getlarge/Cosmonode_PCBs/Cosmonode_ext02/docs/Cosmonode_ext02.png

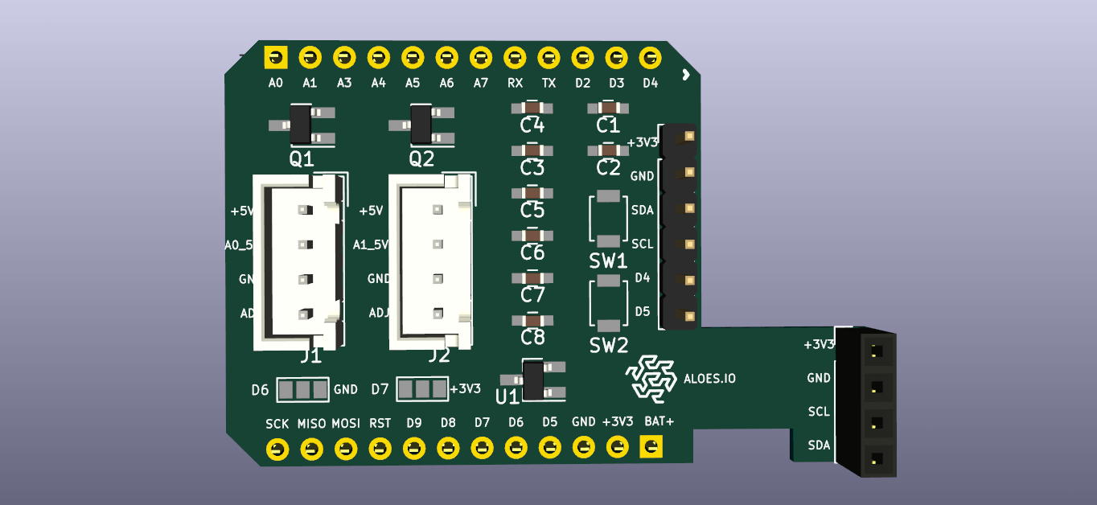
Cosmonode_ext02/docs/Cosmonode_ext02.png
