getlarge/Cosmonode_PCBs/Cosmonode_ext03/docs/Cosmonode_ext03.png

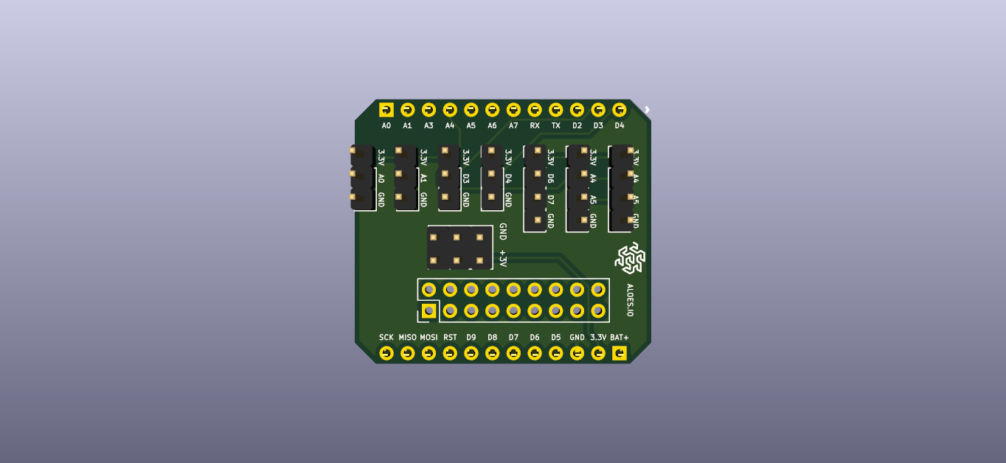
Cosmonode_ext03/docs/Cosmonode_ext03.png
