getlarge/Cosmonode_PCBs/Cosmonode_ext04/Cosmonode_ext_04.png

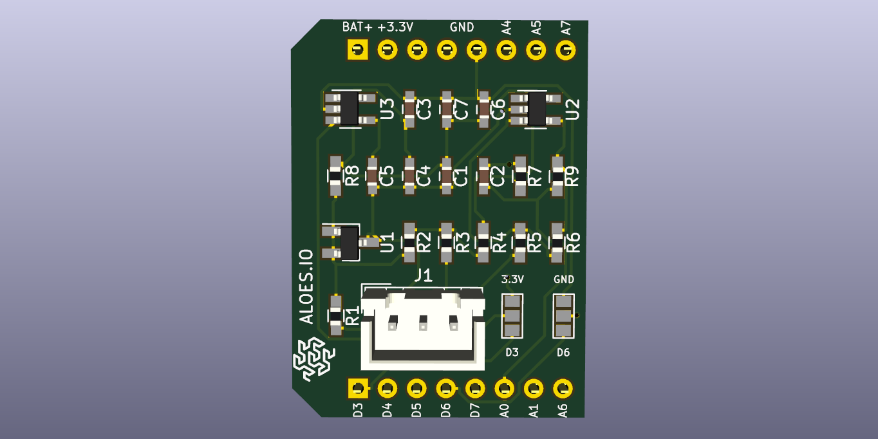
Cosmonode_ext04/Cosmonode_ext_04.png
