getlarge/Cosmonode_PCBs/Cosmonode_ext05/Cosmonode_ext05.png

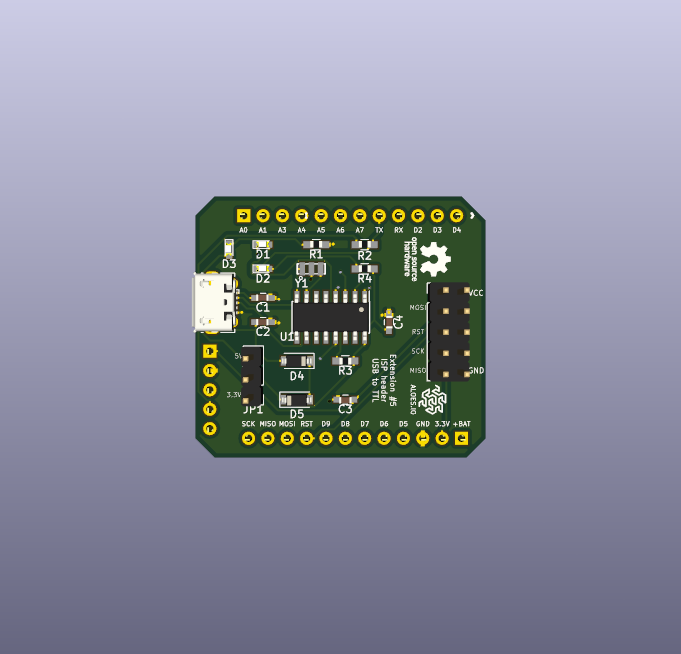
Cosmonode_ext05/Cosmonode_ext05.png
