getlarge/Cosmonode_PCBs/Cosmonode_ext06/Cosmonode_ext06.png

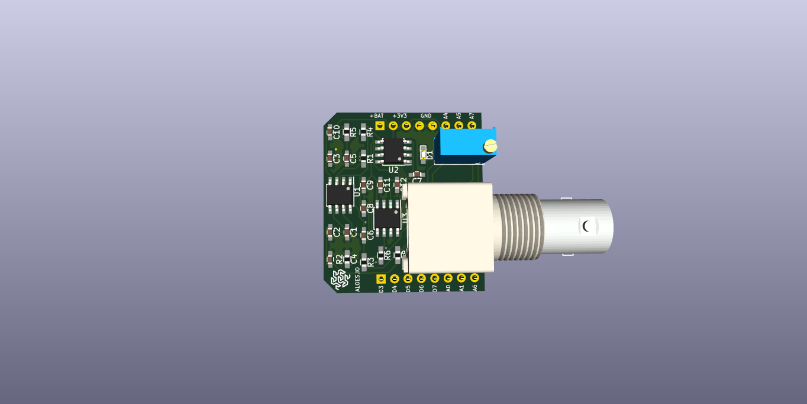
Cosmonode_ext06/Cosmonode_ext06.png
