getlarge/Cosmonode_PCBs/Cosmonode_ext07/Cosmonode_ext07.png

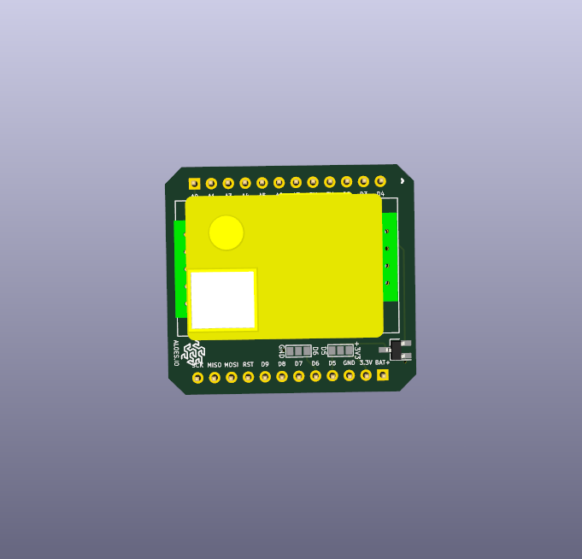
Cosmonode_ext07/Cosmonode_ext07.png
