getlarge/Cosmonode_PCBs/Cosmonode/docs/pcb.pdf

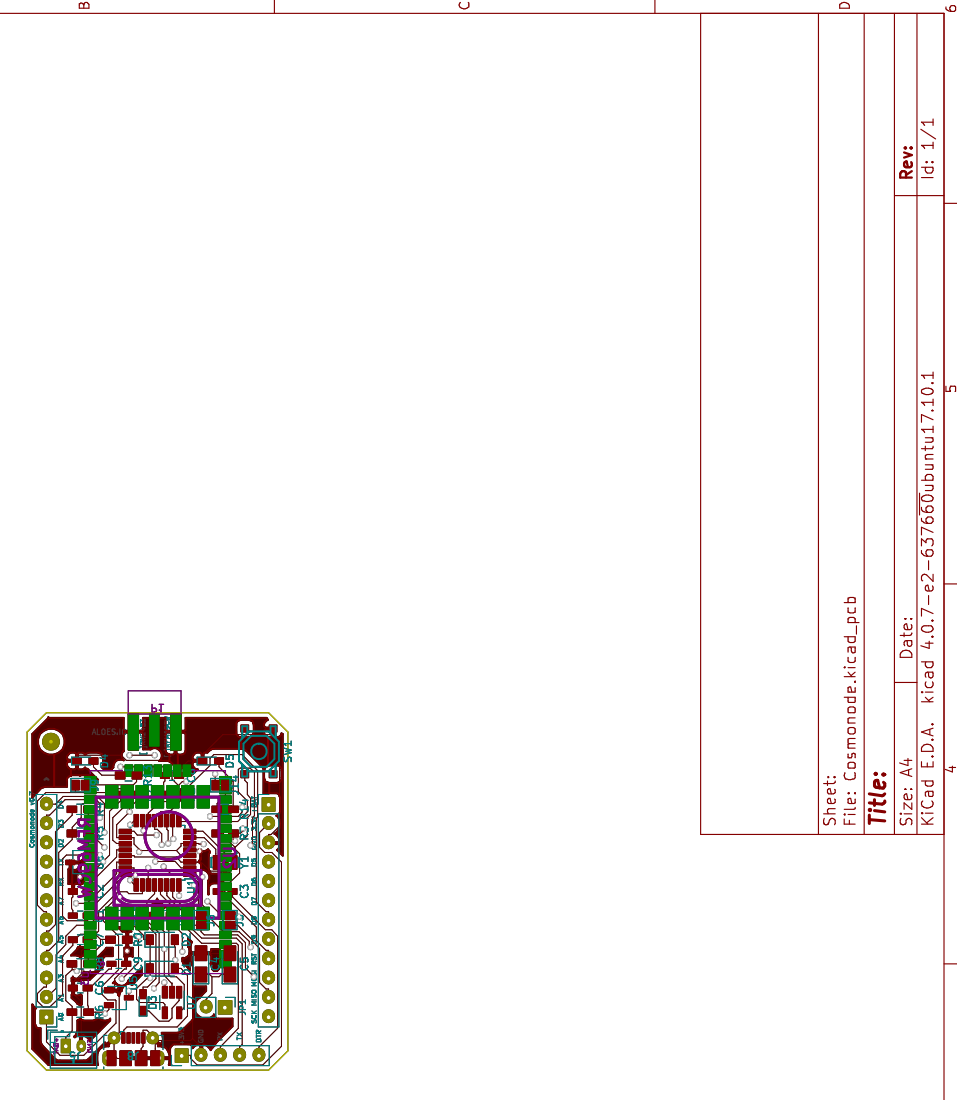
[picture p26: page 1]
