getlarge/Cosmonode_PCBs/Cosmonode/docs/schema.pdf

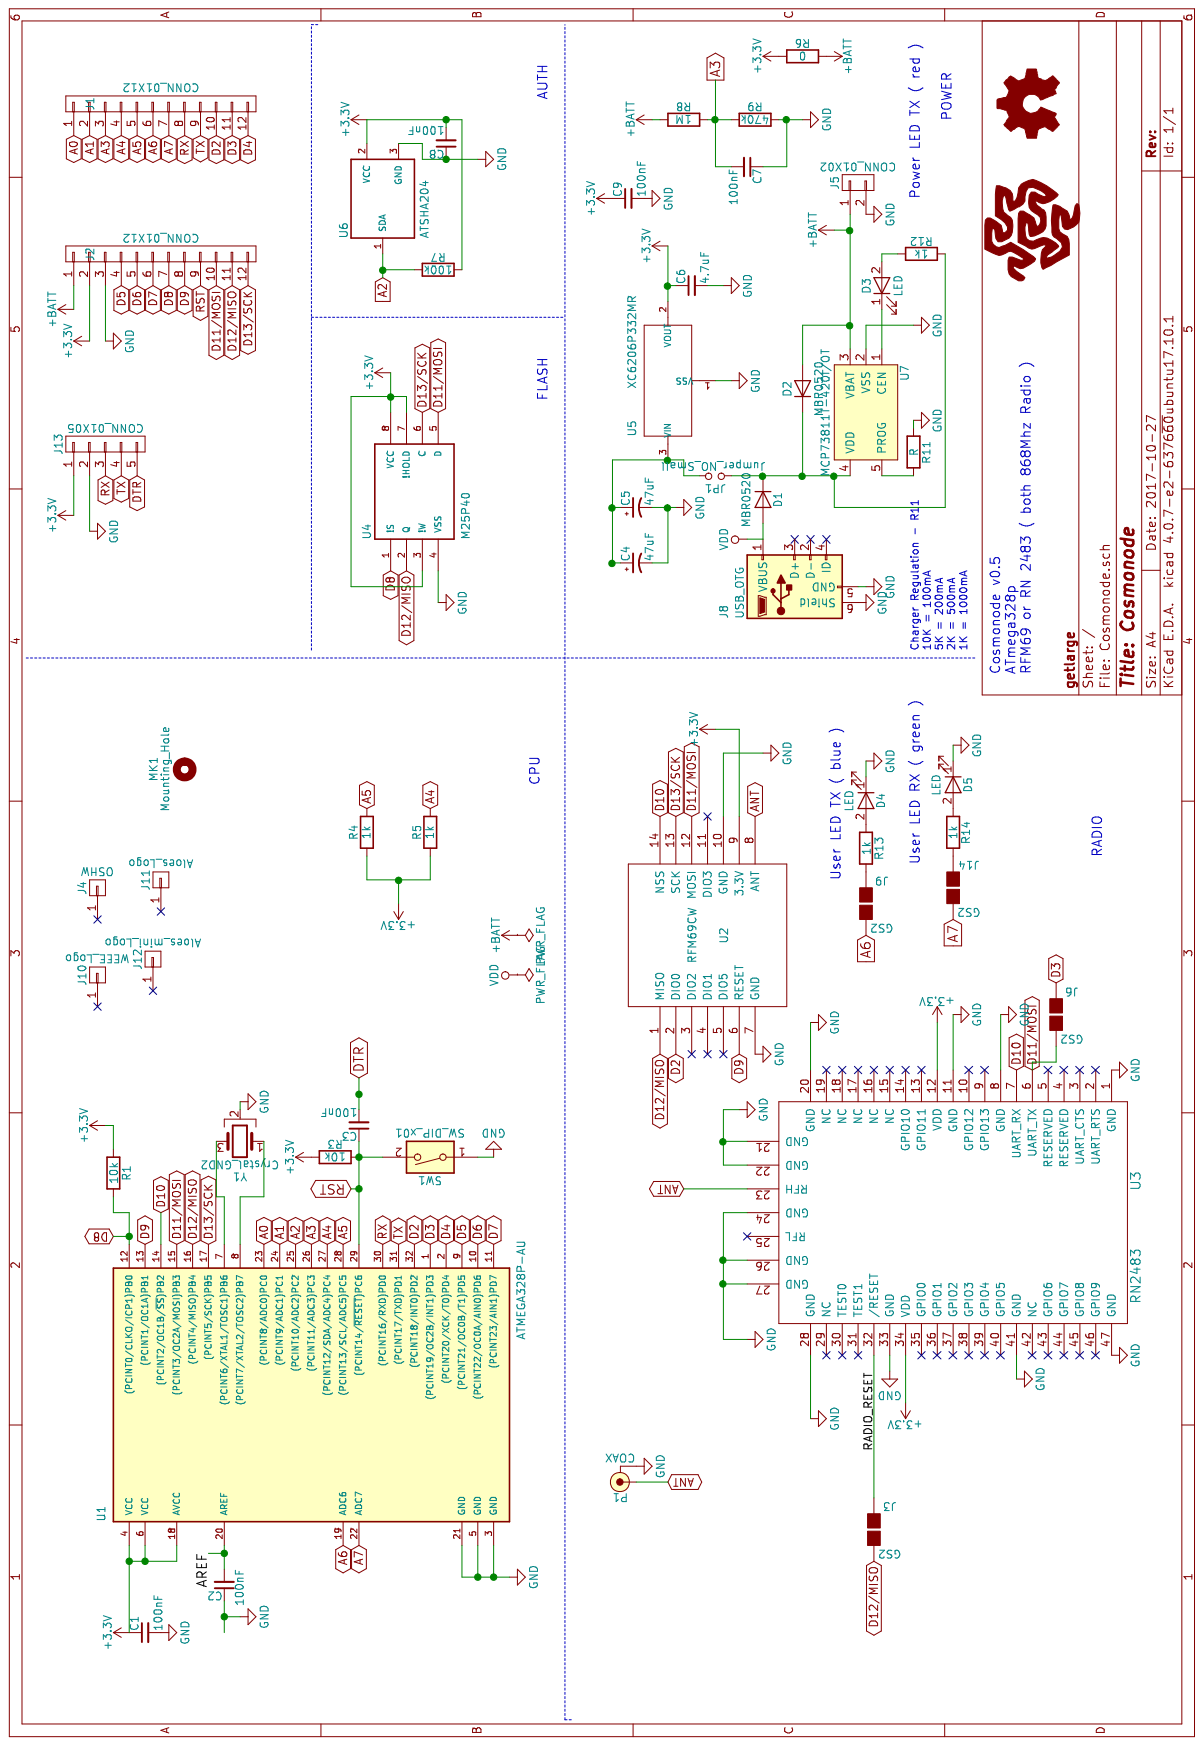
[picture p27: page 1]
