getlarge/Cosmonode_PCBs/Cosmonode_ext03/docs/schema.pdf

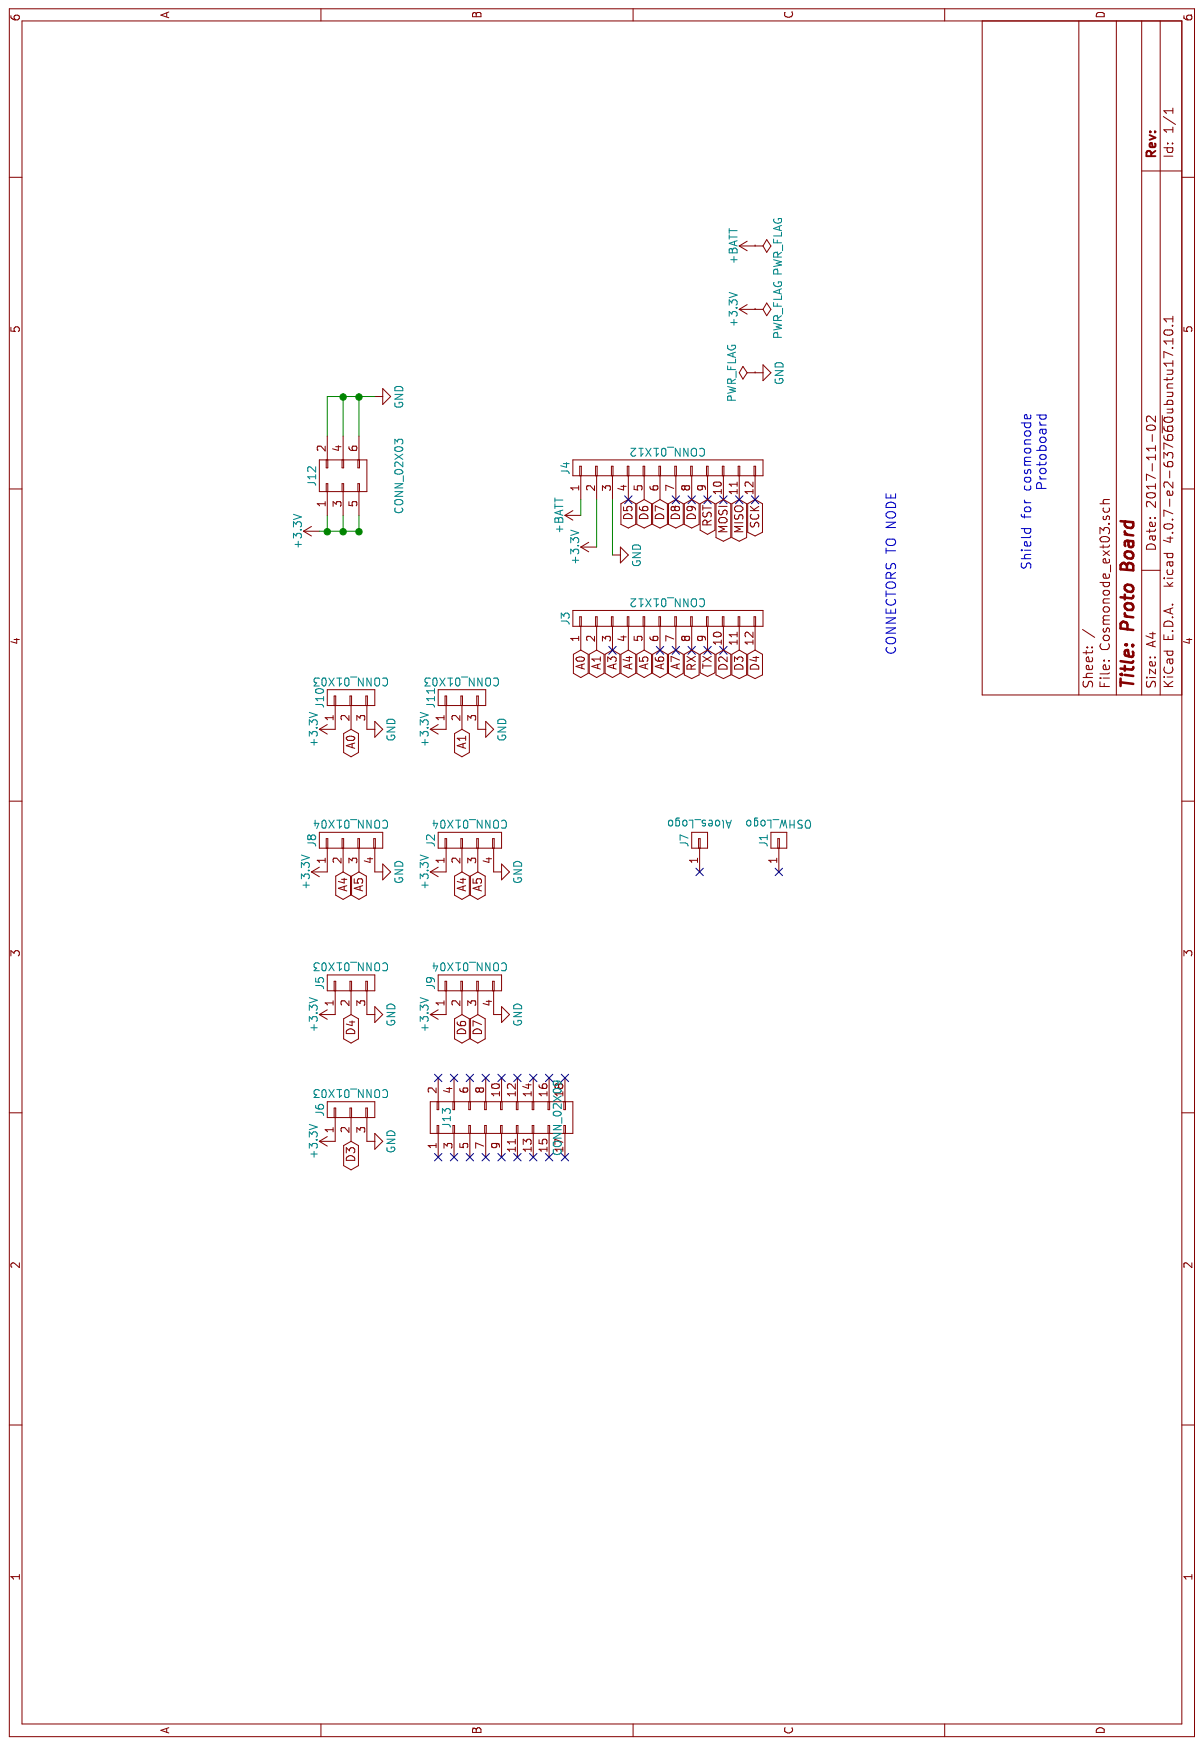
[picture p28: page 1]
