getlarge/Cosmonode_PCBs/Cosmonode_ext02/docs/schema.pdf

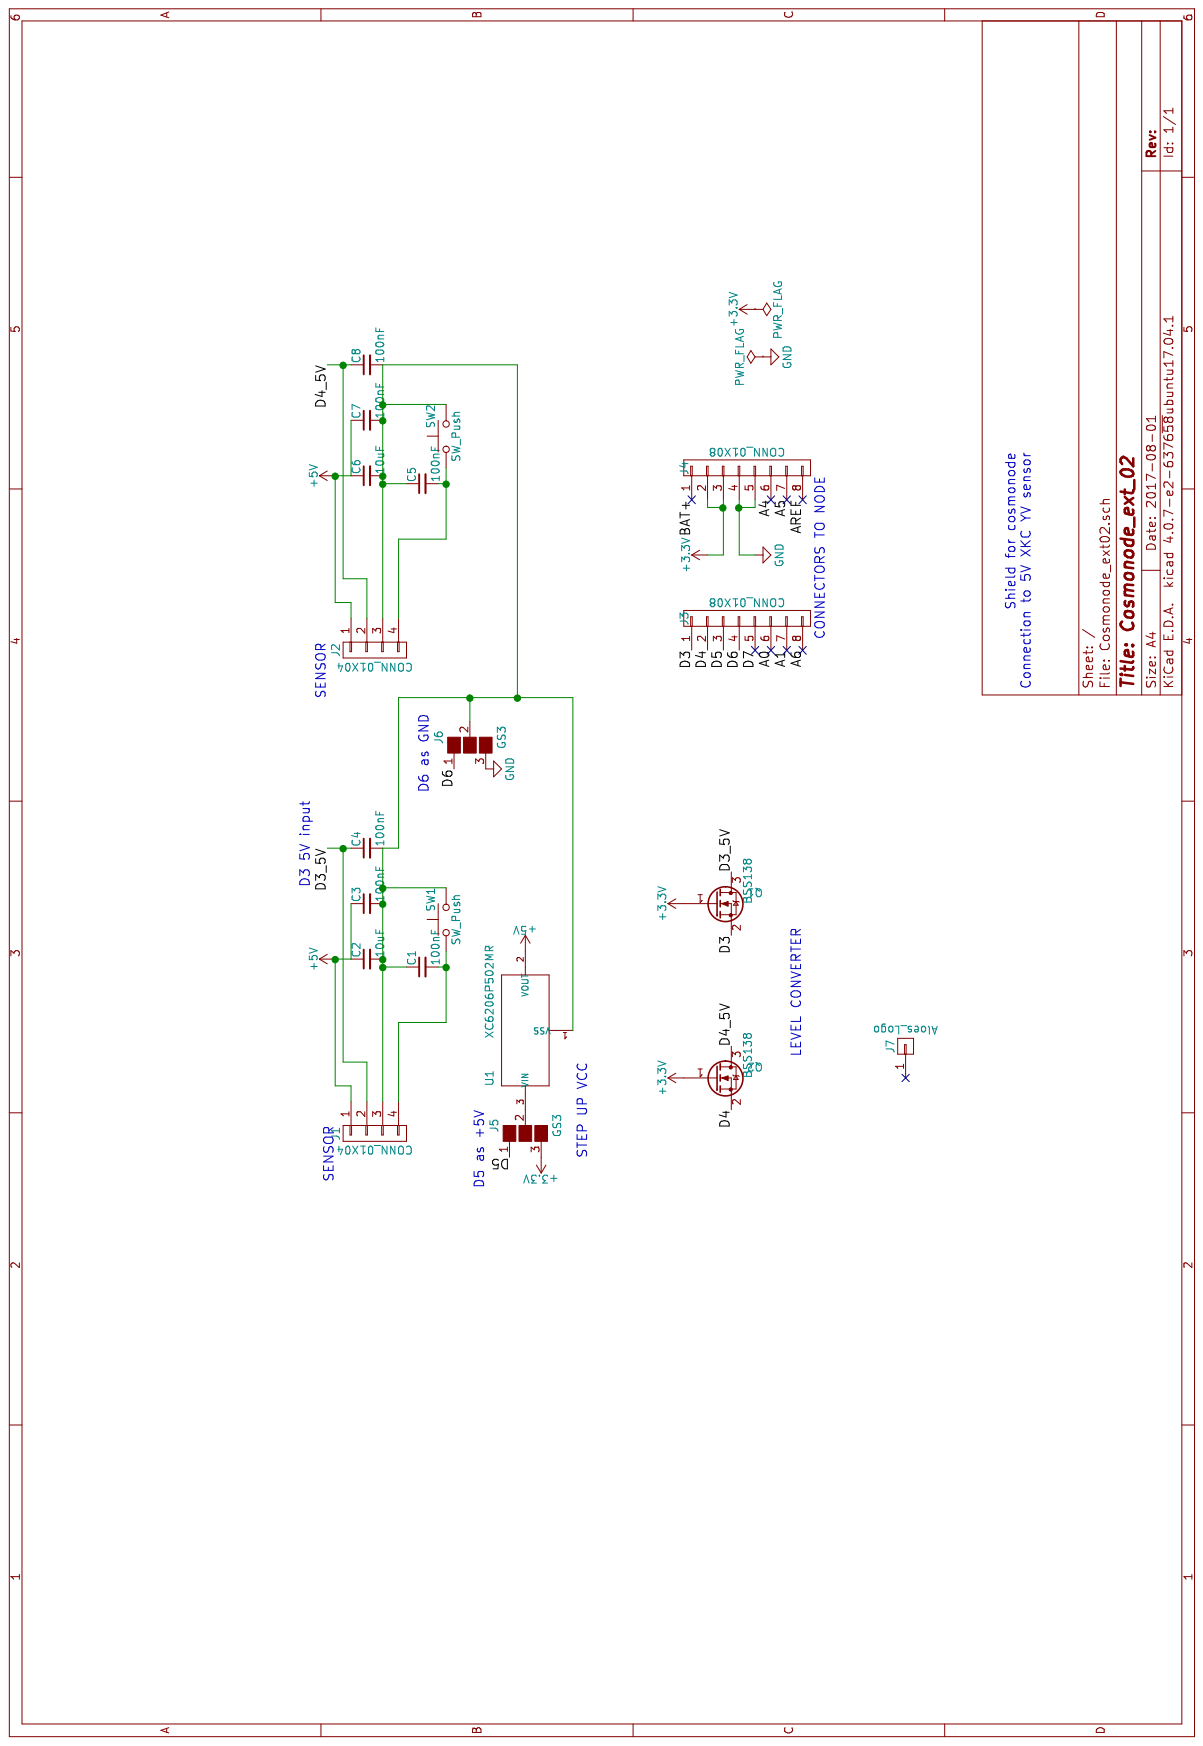
[picture p29: page 1]
